Robomaster-Group-2/RM2025-Internal-Template/RM2025-Internal-Core/Diagnostic/Hook.cpp

/**
 * @file Hook.cpp
 * @author JIANG Yicheng  RM2023 (EthenJ@outlook.sg)
 * @brief For system's error catch and handling
 * @version 0.1
 * @date 2022-08-20
 *
 * @copyright Copyright (c) 2022
 *
 */

#include "DJIMotor.hpp"
#include "FreeRTOS.h"
#include "task.h"

#define GG()     \
    while (true) \
    __asm volatile("bkpt")

namespace Diagnostic
{

/**
 * @brief This function will be called when any fatal error occurs.
 */
static inline void stopAllMotors()
{
    /**
     * @todo    try your best to stop your robot to avoid any damage
     * @hint    you can try to set all the motors' current / voltage to 0, do
     * not forget to send this command.
     */
}

extern "C"
{
    void vApplicationStackOverflowHook(TaskHandle_t xTask, char *pcTaskName)
    {
        stopAllMotors();

        GG();  // One of your tasks has stack overflow hence we stop your code
               // here
        /**
         *      To solve this problem, you may try to:
         *          1. Increase the stack size of the task
         *          2. Check if you have any recursive function
         **/
    }

    void vApplicationTaskReturnHook(void)
    {
        stopAllMotors();

        GG();  // One of your tasks has returned hence we stop your code here
        /**
         *      To solve this problem, you may try to:
         *          1. Check whether you have the infinite loop in your task
         *          2. Check whether you have statement that may cause the task
         *to return (eg. return, break)
         **/
    }

    void vApplicationMallocFailedHook(void)
    {
        stopAllMotors();

        GG();  // Memory allocation failed hence we stop your code here
        /**
         *      We do not allow you to use dynamic memory allocation in the
         *internal competition and further development
         **/
    }

    void __cxa_pure_virtual(void)
    {
        stopAllMotors();

        GG();  // You have called a pure virtual function
        /**
         *      What are you doing??? How you pass the compilation???? Check
         *your code!!!
         **/
    }

    void assertFailed(uint8_t *file, uint32_t line)
    {
        stopAllMotors();

        // Assertion failed hence we stop your code here
        /**
         *      To solve this problem, you may try to:
         *          1. Check whether you used the wrong FreeRTOS API (eg. ISR
         *API in task)
         *          2. Check whether you passed the wrong parameter to the
         *FreeRTOS API
         *          3. Check whether you used FreeRTOS API in a wrong way (eg.
         *use xTaskCreateStatic() in ISR)
         *          4. Check whether you used FreeRTOS API in ISR whose priority
         *is too high (check CubeMX)
         **/
    }

    __attribute__((weak)) void assert_failed(uint8_t *file, uint32_t line)
    {
        assertFailed(file, line);
        __asm volatile("bkpt");
    }

    void hardFault(void)
    {
        stopAllMotors();

        GG();  // Hard fault occurred hence we stop your code here
        /**
         *     To solve this problem, you may try to:
         *          1. Check whether you accessed the memory out of range
         * (especially arrays)
         *          2. Check whether you have accessed a null pointer
         *          3. Check whether you have made illegal register operation
         *          4. Check whether you have create a critical section that is
         * too long
         *
         *     Notice:
         *          1. Divide by zero should not cause hard fault on STM32
         * without specific configuration
         */
    }
}
}  // namespace Diagnostic
